nstrappazzonc/CH9141/img/connection.kicad_sch

## KiCad design img/connection.kicad_sch (2024-01-03)

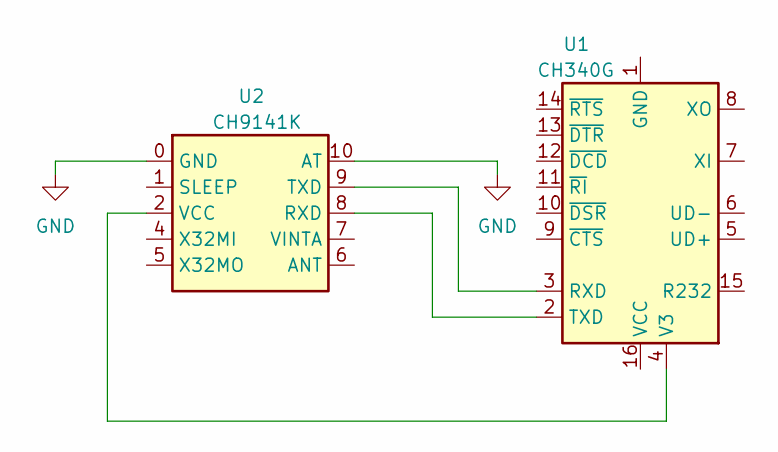
[picture p4: schematic connection.kicad_sch]

Parts:
U1: CH340G; SOIC-16_3.9x9.9mm_P1.27mm
U2: CH9141K; SSOP-10_3.9x4.9mm_P1.00mm

Connections:
GND: U2.0 (GND), U2.10 (AT)
unnamed: U1.2 (TXD), U2.8 (RXD)
unnamed: U1.3 (RXD), U2.9 (TXD)
unnamed: U1.4 (V3), U2.2 (VCC)
